0x007E/blr/BLR.asc

D1: LED; Red
D2: LED; Yellow
D3: LED; Green
R1: res; 4k7
R2: res; 12k
R3: res; 10k
R4: res; 38k
R5: res; 40k
R6: res; 1k
R7: res; 1k
R8: res; 1k
R9: res; 1k
R10: res; 1k
R11: res; 1Meg
R12: res; 1Meg
U1: OP07
U2: OP07
V1: voltage; PWL(0 9 100m 13.7 200m 9)
V2: voltage; 2.5
Named nets: VCC, 0, uOUT
.tran 200m
.MODEL Red D (IS=93.1P RS=42M N=4.61 BV=4 IBV=10U CJO=2.97P VJ=.75 M=.333 TT=4.32U type=LED)
.MODEL Yellow D (IS=93.1P RS=42M N=5.61 BV=4 IBV=10U CJO=2.97P VJ=.75 M=.333 TT=4.32U type=LED)
.MODEL Green D (IS=93.1P RS=42M N=4.61 BV=4 IBV=10U CJO=2.97P VJ=.75 M=.333 TT=4.32U type=LED)
